formalism/zturn-adc-fm-rx/FPGA/adc_capture/mys-xc7z020-trd.srcs/sources_1/imports/hdl/bram.vhd

library IEEE;
use IEEE.std_logic_1164.all;
use IEEE.std_logic_arith.all;
use IEEE.std_logic_unsigned.all;

entity bram is
  port (
    clk         :       in      std_logic;
    adr         :       in      std_logic_vector(31 downto 0);
    data        :       out     std_logic_vector(31 downto 0)   :=      (others => '0')
    );
end bram;

architecture rtl of bram is
  type  memtp is array (0 to 399) of std_logic_vector(31 downto 0);
  constant      mem     :       memtp   :=
    (X"00001000",
       X"0AC40BD5",
       X"0FED0181",
       X"0CCBF665",
       X"02FFF049",
       X"F7A4F25C",
       X"F0A3FB8A",
       X"F1A20709",
       X"FA1D0EE0",
       X"05A70EF7",
       X"0E410743",
       X"0F6EFBC8",
       X"0892F27E",
       X"FD40F03D",
       X"F35CF632",
       X"F00D0141",
       X"F50D0BA9",
       X"FFC00FFF",
       X"0A940C00",
       X"0FE701C1",
       X"0CF1F699",
       X"033EF056",
       X"F7DBF23B",
       X"F0B6FB4C",
       X"F18606CF",
       X"F9E10EC8",
       X"056B0F0D",
       X"0E23077C",
       X"0F7FFC06",
       X"08C8F2A1",
       X"FD80F033",
       X"F384F600",
       X"F0090101",
       X"F4DE0B7D",
       X"FF800FFD",
       X"0A640C2A",
       X"0FDF0201",
       X"0D17F6CD",
       X"037DF063",
       X"F813F21B",
       X"F0C9FB0F",
       X"F16B0695",
       X"F9A60EAF",
       X"052E0F23",
       X"0E0507B5",
       X"0F8EFC44",
       X"08FEF2C5",
       X"FDBFF029",
       X"F3ACF5CE",
       X"F00500C0",
       X"F4B00B50",
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
       X"0F5DFB8A",
       X"085CF25C",
       X"FD01F049",
       X"F335F665",
       X"F0130181",
       X"F53C0BD5"
      );
  begin

    process (clk) begin
       if (rising_edge(clk)) then
          data  <=      mem(CONV_INTEGER(adr));
       end if;
    end process;
  end rtl;
