formalism/zturn-adc-fm-rx/FPGA/adc_capture/mys-xc7z020-trd.srcs/sources_1/new/fm_stereo_pll.vhd

library IEEE;
use IEEE.STD_LOGIC_1164.ALL;
use IEEE.STD_LOGIC_ARITH.ALL;
use IEEE.STD_LOGIC_SIGNED.ALL;
library UNISIM;
use UNISIM.VCOMPONENTS.ALL;

entity fm_stereo_pll is
	port (
		clk			:	in	std_logic;
		en			:	in	std_logic;
		atan_diff	:	in	std_logic_vector(31 downto 0);

		sin38khz	:	out	std_logic_vector(11 downto 0)
	);
end fm_stereo_pll;

architecture STRUCTURE of fm_stereo_pll is
	constant PINC_MAX		:	std_logic_vector(20 downto 0)	:=	'0' & X"14000";
	constant PINC_MIN		:	std_logic_vector(20 downto 0)	:=	'0' & X"13000";

	signal	r_pinc			:	std_logic_vector(20 downto 0)	:=	'0' & X"1374B";		-- nearly 19kHz
	signal	r_config_tvalid	:	std_logic						:=	'0';
	signal	w_data			:	std_logic_vector(31 downto 0);
	signal	w_sin			:	std_logic_vector(9 downto 0);
	signal	w_cos			:	std_logic_vector(9 downto 0);
	signal	w_dds_tvalid	:	std_logic;
	signal	w_fir_tready	:	std_logic;
	signal	r_en			:	std_logic;
	signal	r_en_cnt		:	std_logic_vector(7 downto 0)	:=	(others => '0');

	signal	r_mul			:	std_logic_vector(33 downto 0);
	signal	w_fir_tdata_in	:	std_logic_vector(31 downto 0);
	signal	w_fir_tdata_out	:	std_logic_vector(31 downto 0);
	signal	w_fir_tvalid	:	std_logic;

	signal	r_sum			:	std_logic_vector(31 downto 0)	:=	(others => '0');

begin

	w_sin			<=		w_data(25 downto 16);
	w_cos			<=		w_data(9 downto 0);

	dds_i		:	entity work.dds_fm_pilot 
	port map (
		aclk					=>		clk,
		s_axis_config_tvalid	=>		r_config_tvalid,
		s_axis_config_tdata		=>		X"070000" & "000" & r_pinc,		-- [44:24] POFF, [20:0] PINC ufix21_21
		m_axis_data_tvalid		=>		w_dds_tvalid,
		m_axis_data_tready		=>		en,
		m_axis_data_tdata		=>		w_data,
		m_axis_phase_tvalid		=>		open,
		m_axis_phase_tready		=>		en,
		m_axis_phase_tdata		=>		open
	);

	-- mixer
	process (clk) begin
		if (rising_edge(clk)) then
			if (en = '1') then
				r_mul		<=	atan_diff(31 downto 8) * w_cos;			-- 24+10=34bits
			else
				r_mul		<=	r_mul;
			end if;

			r_en		<=	en;
			if (en = '1' and r_en_cnt >= 4) then
				r_en_cnt	<=	(others => '0');
			elsif (en = '1') then
				r_en_cnt	<=	r_en_cnt + 1;
			else
				r_en_cnt	<=	r_en_cnt;
			end if;

			if (en = '1' and r_en_cnt >= 4) then
				r_config_tvalid	<=	'1';

				-- pinc frequency resolution is 0.4Hz
				if (r_sum < 0) then
					if (r_pinc < PINC_MAX) then
						r_pinc	<=	r_pinc + 1;
					else
						r_pinc	<=	r_pinc;
					end if;
				else
					if (r_pinc > PINC_MIN) then
						r_pinc	<=	r_pinc - 1;
					else
						r_pinc	<=	r_pinc;
					end if;
				end if;
			else
				r_config_tvalid	<=	'0';
				r_pinc			<=	r_pinc;
			end if;

		end if;
	end process;

	w_fir_tdata_in		<=	r_mul(33 downto 2);		-- TODO

	-- 500kHz * 0.04 = 20kHz
	fir_i	:	entity work.fir_lpf_20khz 
	port map (
		aclk				=>		clk,
		s_axis_data_tvalid	=>		r_en,
		s_axis_data_tready	=>		w_fir_tready,
		s_axis_data_tdata	=>		w_fir_tdata_in,		-- 24 bit
		m_axis_data_tvalid	=>		w_fir_tvalid,
		m_axis_data_tdata	=>		w_fir_tdata_out
	);

	process (clk) begin
		if (rising_edge(clk)) then
			if (w_fir_tvalid = '1' and r_en_cnt = 0) then
				r_sum	<=	w_fir_tdata_out;
			elsif (w_fir_tvalid = '1') then
				r_sum	<=	r_sum + w_fir_tdata_out;
			else
				r_sum	<=	r_sum;
			end if;
		end if;
	end process;

end STRUCTURE;
